ArtemZaZ/CupRtc/keil/src/main/cspeexparser.h

#ifndef CSPEEXPARCER_H
#define CSPEEXPARCER_H

#include "stdint.h"
#define MAX_TEXT_SIZE       100
#define SPEEX_BLOCK_SIZE    20

#define NUM_FRAME_ADDRESS 0x0000
#define NUM_TEXT_ADDRESS 0x0020
#define TEXT_ADDRESS  0x0040
#define NUMB_OF_TEXT  10
#define SPEEX_ADDRESS 0x0180

typedef struct
{
  uint16_t checksum;  // избыточный код
  uint8_t descriptor;       // дескриптор пакета
  uint16_t data;      // количество блоков
} BlocksPackage;

typedef struct
{
  uint16_t checksum;  // избыточный код
  uint8_t descriptor;       // дескриптор пакета
  uint8_t textnum;    // номер текста
  uint8_t text[MAX_TEXT_SIZE];   // сам текст, в конце нуль-терминальная строка
} TextPackage;

typedef struct
{
  uint16_t checksum;  // избыточный код
  uint8_t descriptor;       // дескриптор пакета
  uint8_t data[SPEEX_BLOCK_SIZE];   // speex данные
} SpeexPackage;

typedef struct
{
  uint16_t checksum;  // избыточный код
  uint8_t descriptor;       // дескриптор пакета
  uint8_t code;   // код обратной связи с пк
} FeedbackPackage;


// принимает пакет и записывает его в один из пакетов state, text или speex, возвращает дескриптор пакета или 0, в случае ошибки
uint8_t recv(void (*readArrayFun)(uint8_t*, uint32_t), BlocksPackage* state, TextPackage* text, SpeexPackage* speex, FeedbackPackage* fb);
// отправляет пакет обратной связи
void sendFeedback(void (*sendArrayFunc)(uint8_t*, uint32_t), uint8_t code);


#endif
