ArtemZaZ/CupRtc/keil/src/main/ws2812b_modes.h

#ifndef WS2812b_MODES_H
#define WS2812b_MODES_H

/*
*Библиотека для включения какого-нибудь режима на светодиодах
*ВНИМАНИЕ
*вся библиотека подстроена под работу с системой freertos
*/

#include <stdint.h>
#include <stdlib.h>
#include <stdio.h>
#include "main/ws2812b.h"
#include "main/Delay.h"
#include "freertos.h"

void Turn_on_Led_mode(uint8_t mode);

#endif
